marzof/fridge-staircase/railing_last_fixing_vsb.dxf

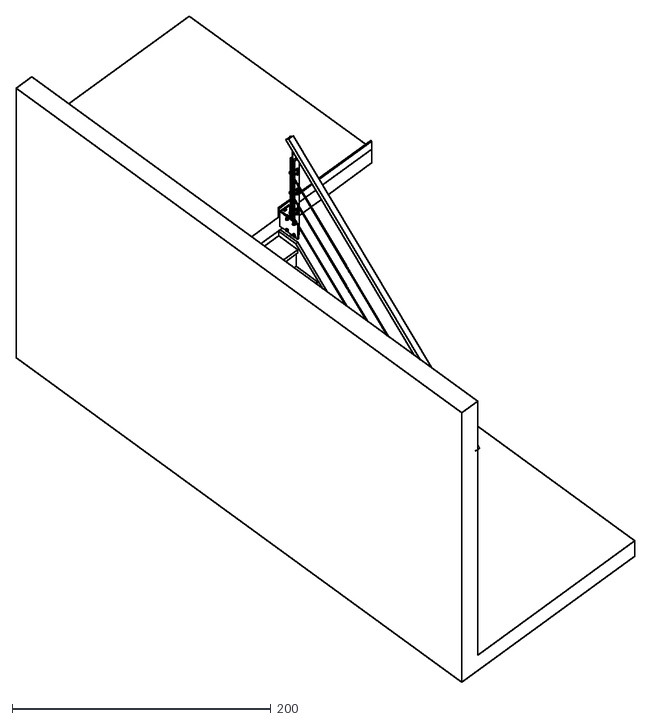
[picture p15: CAD file, 2017-08-27]
railing_last_fixing_vsb.dxf
478.4 x 514.9
