marzof/fridge-staircase/handrail_holder_vsb.dxf

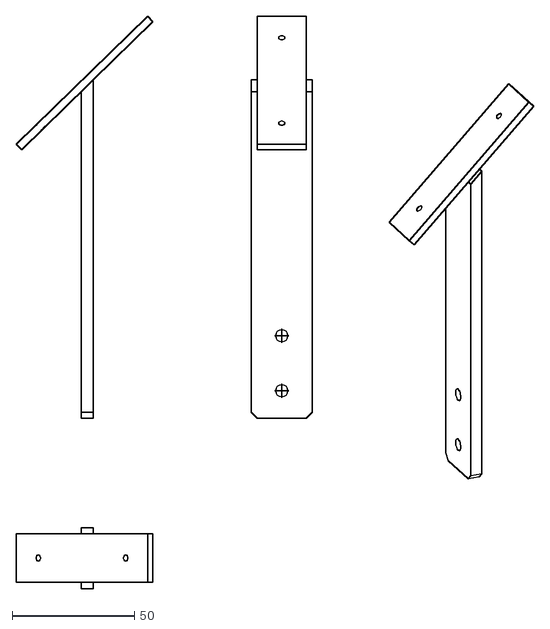
[picture p16: CAD file, 2017-08-27]
handrail_holder_vsb.dxf
211.8 x 234.3
