marzof/fridge-staircase/fasteners.fcstd

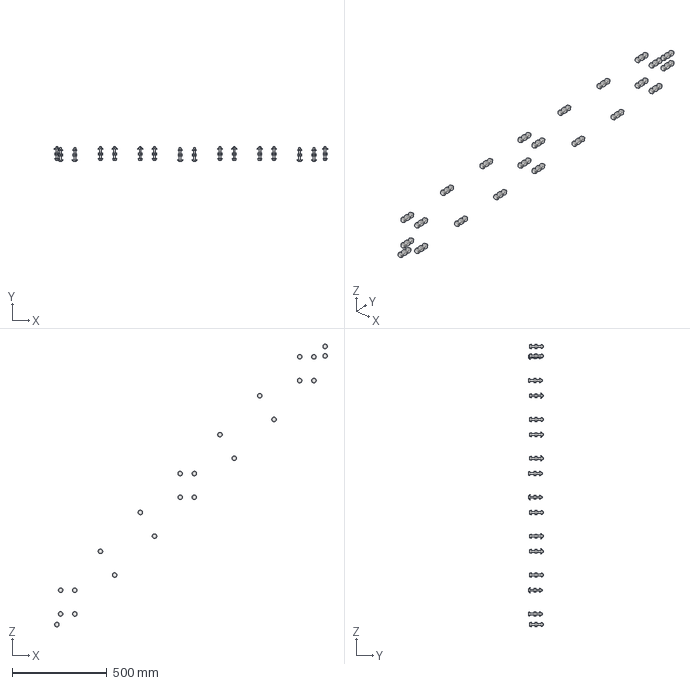
[picture p17: CAD file, 2017-08-27]
fasteners.fcstd
1438.8 x 78.4 x 1491.0 mm
