marzof/fridge-staircase/railing_wood_vsb.dxf

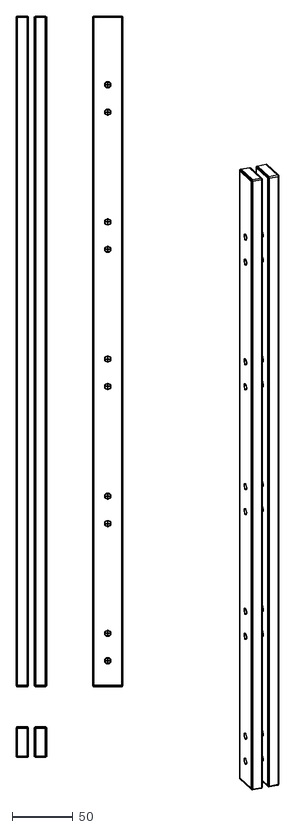
[picture p18: CAD file, 2017-08-27]
railing_wood_vsb.dxf
215.5 x 634.6
