marzof/fridge-staircase/railing_last.fcstd

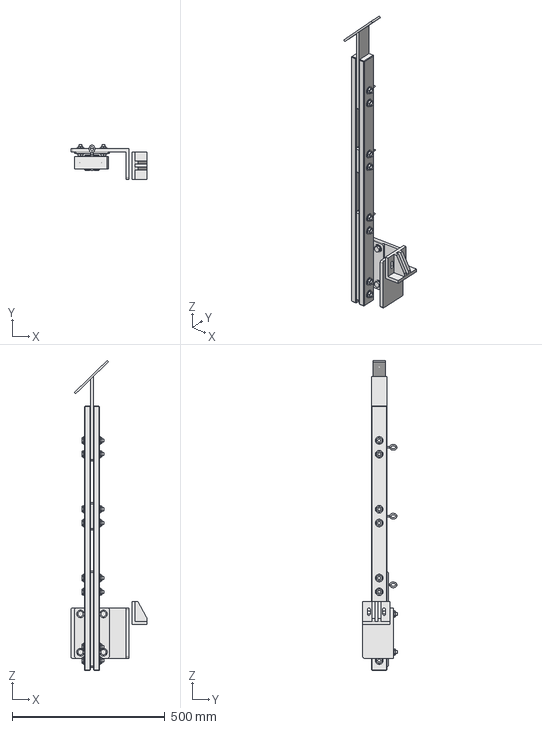
[picture p19: CAD file, 2017-08-27]
railing_last.fcstd
250.0 x 113.0 x 1014.1 mm
