marzof/fridge-staircase/fridge_box_door.fcstd

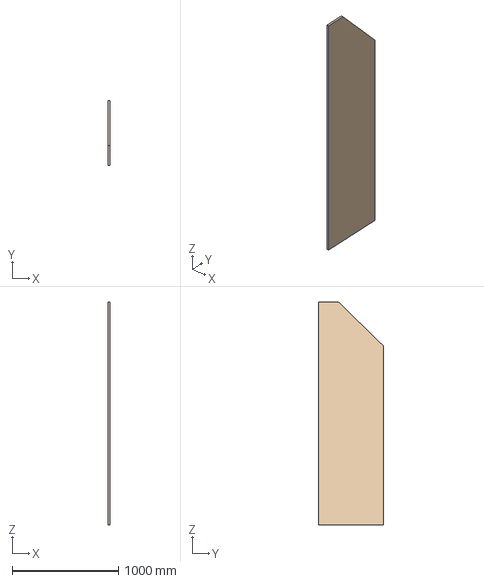
[picture p20: CAD file, 2017-08-27]
fridge_box_door.fcstd
18.0 x 610.0 x 2095.0 mm
