marzof/fridge-staircase/ropes.fcstd

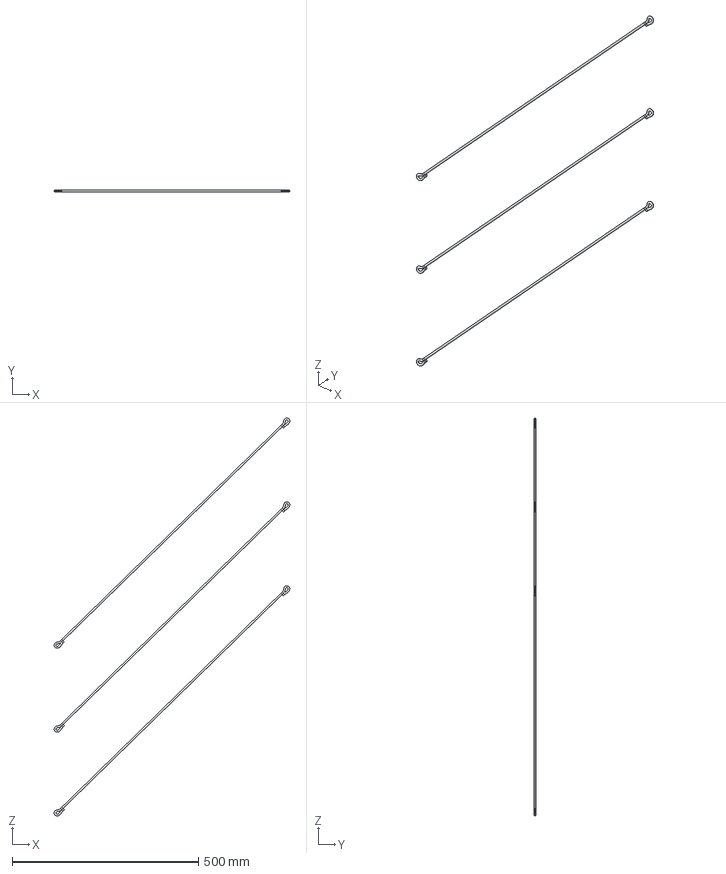
[picture p21: CAD file, 2017-08-27]
ropes.fcstd
632.3 x 5.00 x 1067.7 mm
