marzof/fridge-staircase/stair_profile.fcstd

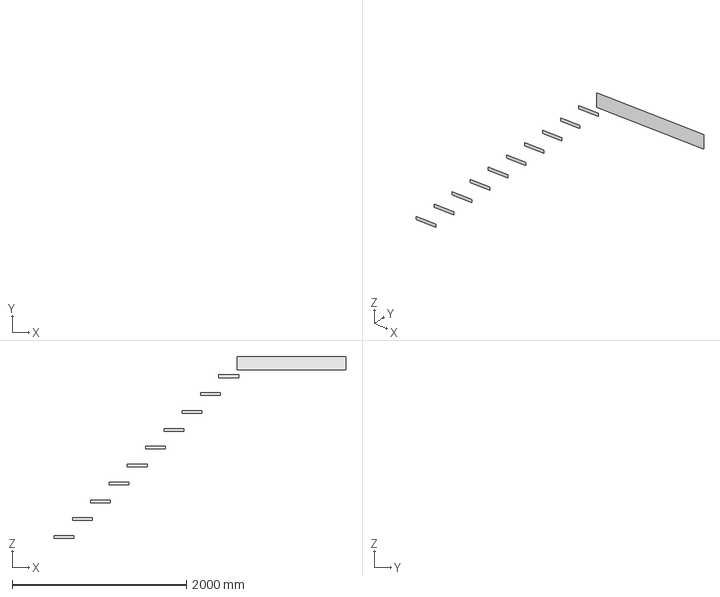
[picture p22: CAD file, 2017-08-27]
stair_profile.fcstd
3350.0 x 6.5e-14 x 2090.0 mm
