marzof/fridge-staircase/railing_front_hdn.dxf

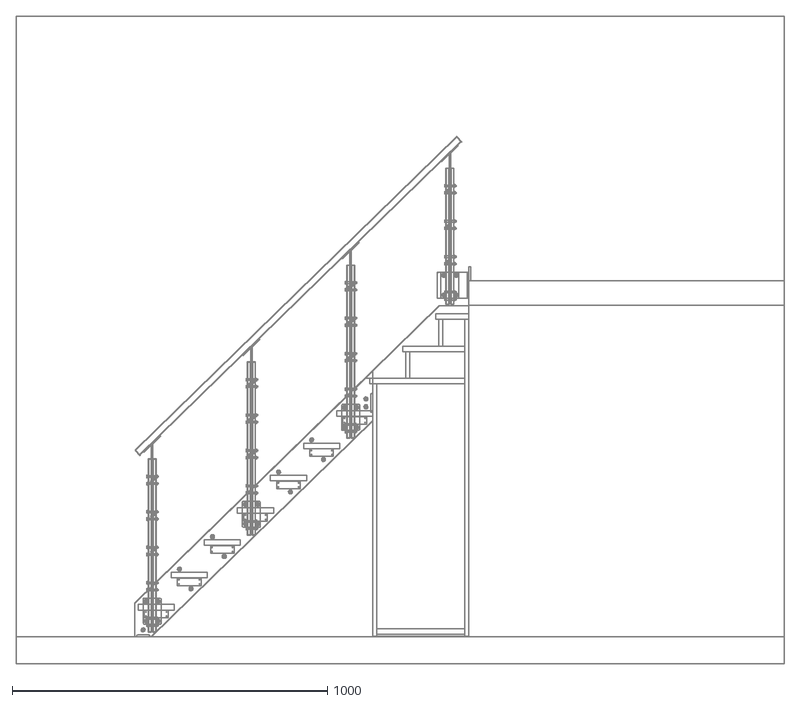
[picture p23: CAD file, 2017-08-27]
railing_front_hdn.dxf
2437.5 x 2056.1
