marzof/fridge-staircase/railing_rear_vsb.dxf

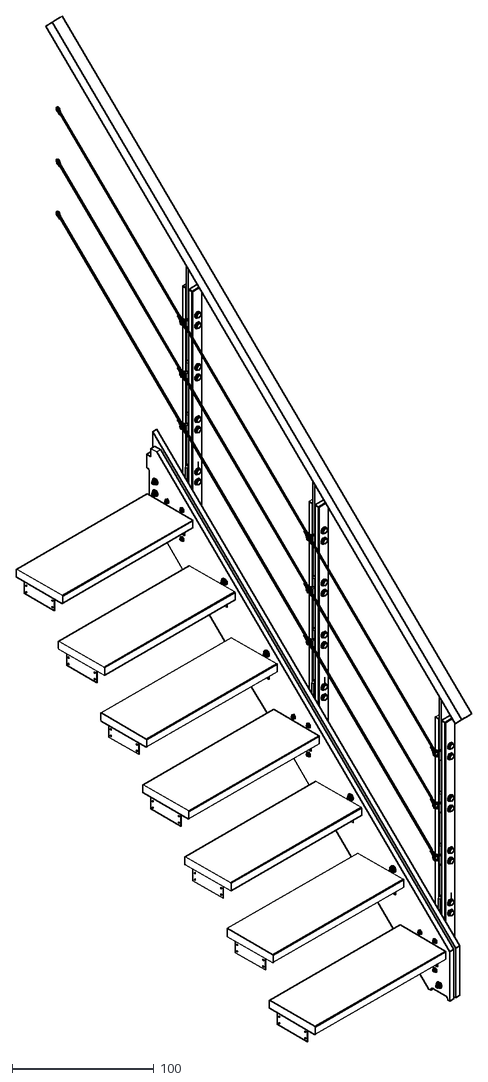
[picture p24: CAD file, 2017-08-27]
railing_rear_vsb.dxf
320.9 x 722.7
