marzof/fridge-staircase/plate.fcstd

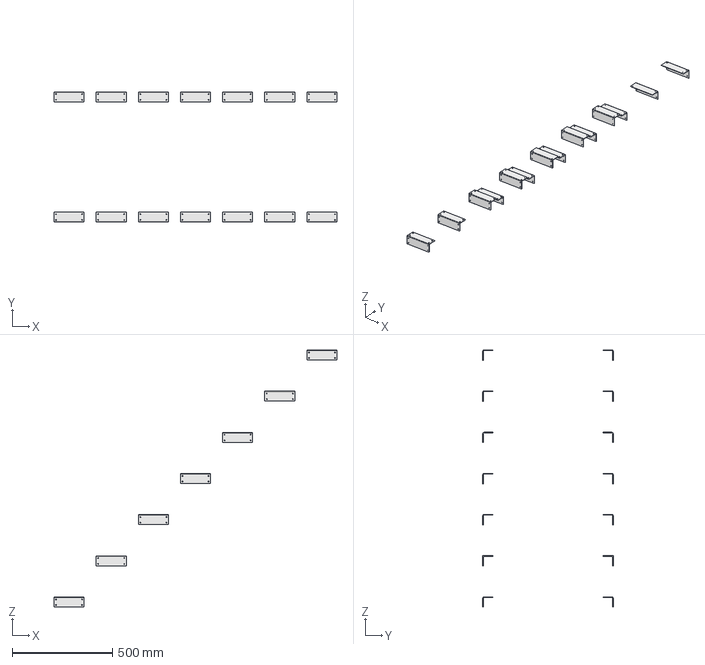
[picture p25: CAD file, 2017-08-27]
plate.fcstd
1410.0 x 650.0 x 1280.0 mm
