marzof/fridge-staircase/railing_wood_hdn.dxf

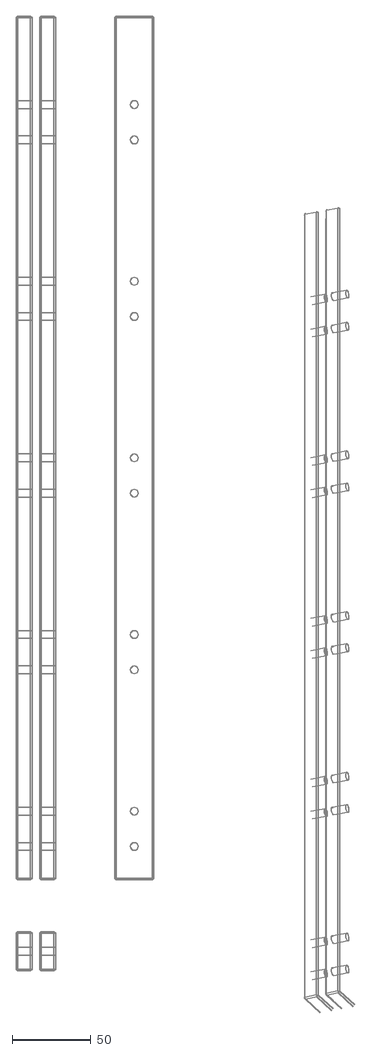
[picture p26: CAD file, 2017-08-27]
railing_wood_hdn.dxf
215.5 x 634.6
