marzof/fridge-staircase/railing_last_elements_hdn.dxf

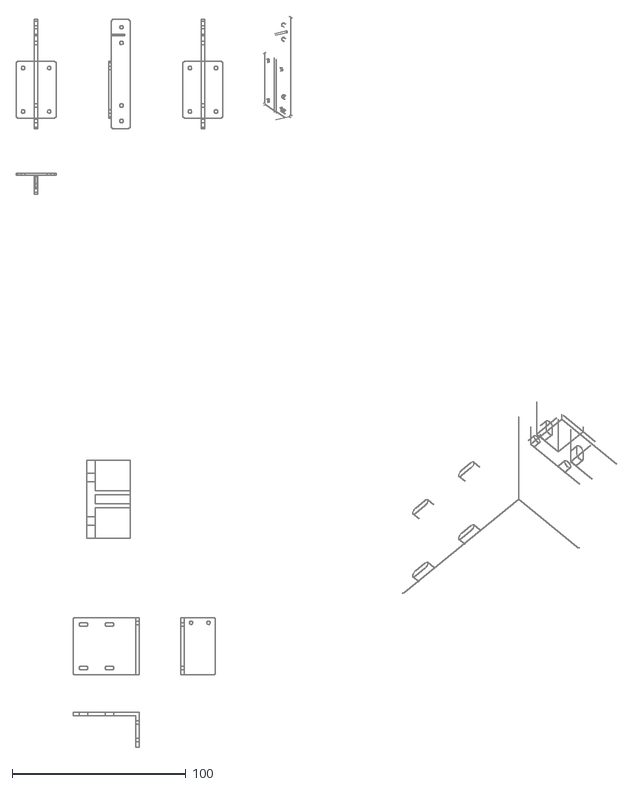
[picture p27: CAD file, 2017-08-27]
railing_last_elements_hdn.dxf
345.8 x 420.8
