marzof/fridge-staircase/railing_last_elements_vsb.dxf

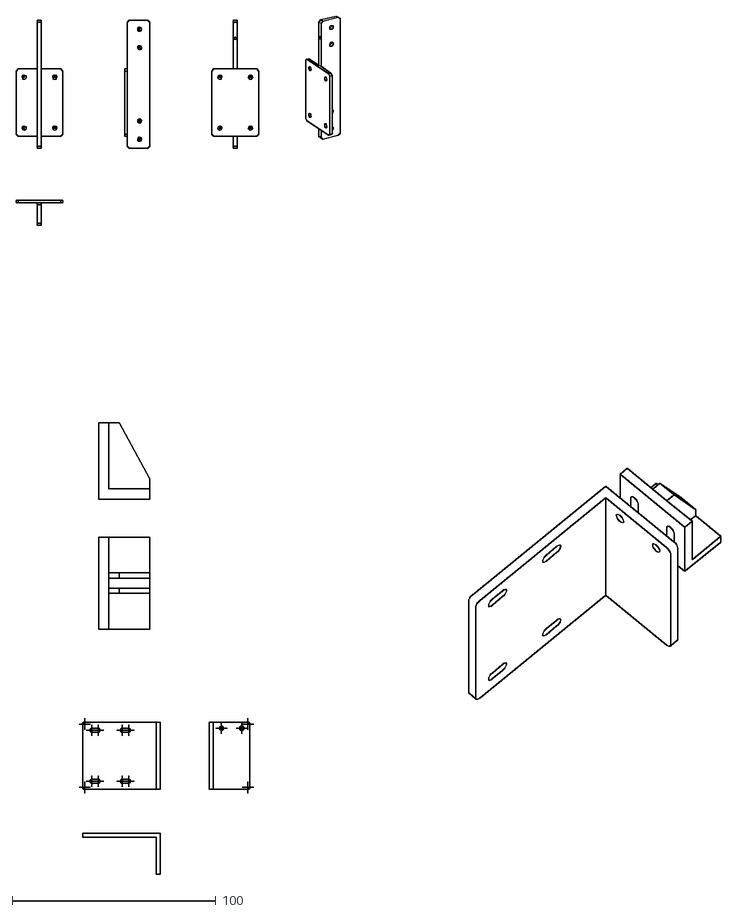
[picture p28: CAD file, 2017-08-27]
railing_last_elements_vsb.dxf
345.8 x 420.8
