marzof/fridge-staircase/railing_plate_hdn.dxf

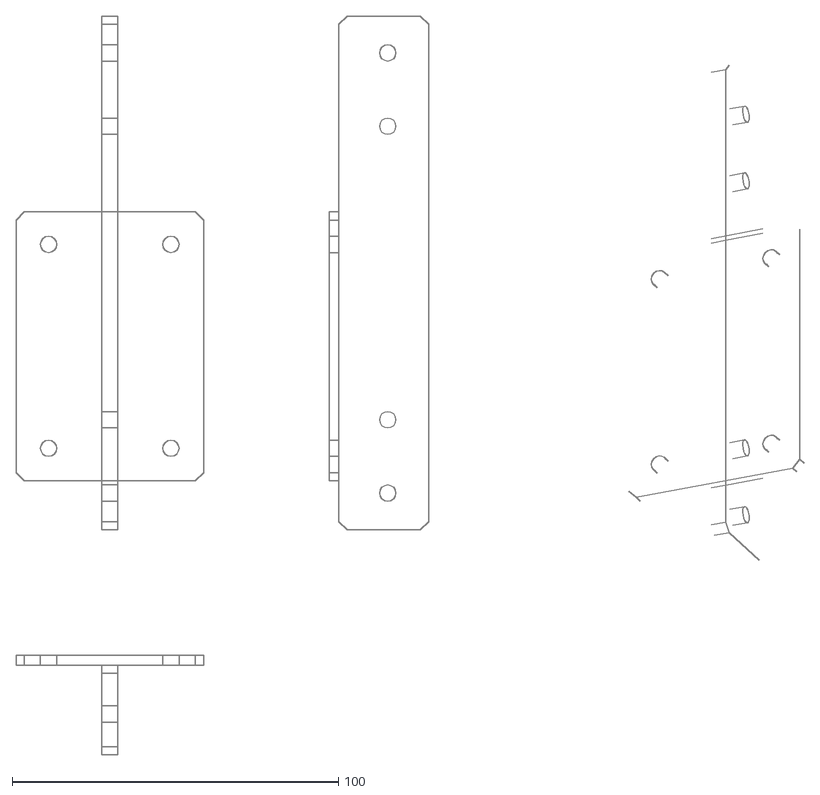
[picture p29: CAD file, 2017-08-27]
railing_plate_hdn.dxf
241.6 x 226.5
