marzof/fridge-staircase/railing_last_fixing_hdn.dxf

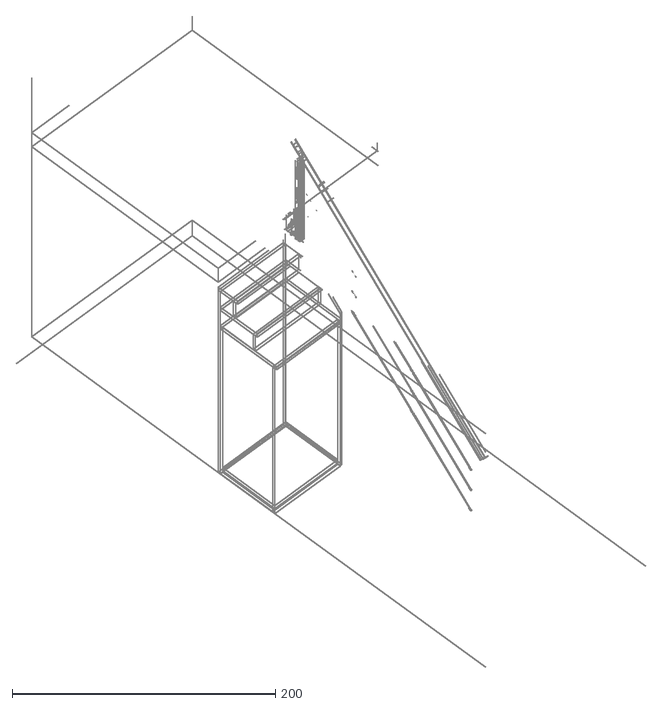
[picture p30: CAD file, 2017-08-27]
railing_last_fixing_hdn.dxf
478.4 x 494.3
