marzof/fridge-staircase/railing_last_wood_hdn.dxf

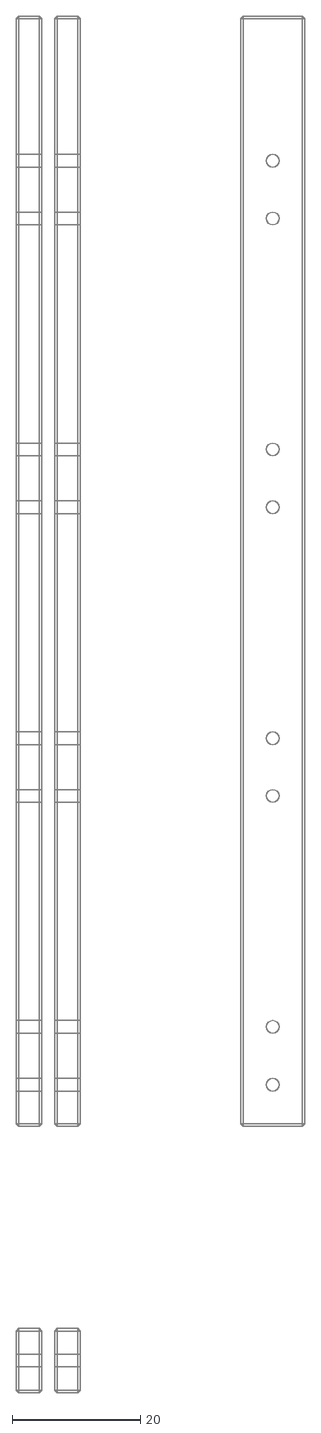
[picture p31: CAD file, 2017-08-27]
railing_last_wood_hdn.dxf
45.0 x 214.5
