marzof/fridge-staircase/loft_ropes.fcstd

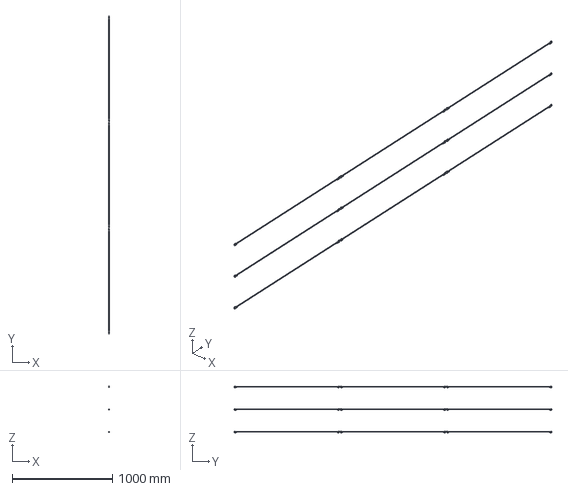
[picture p32: CAD file, 2017-08-27]
loft_ropes.fcstd
5.00 x 3176.2 x 467.0 mm
