marzof/fridge-staircase/railing_wood.fcstd

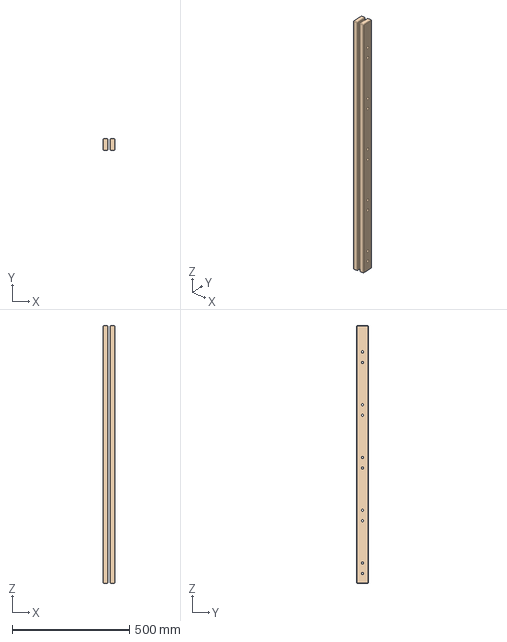
[picture p33: CAD file, 2017-08-27]
railing_wood.fcstd
50.0 x 50.0 x 1100.0 mm
