marzof/fridge-staircase/railing_last_wood.fcstd

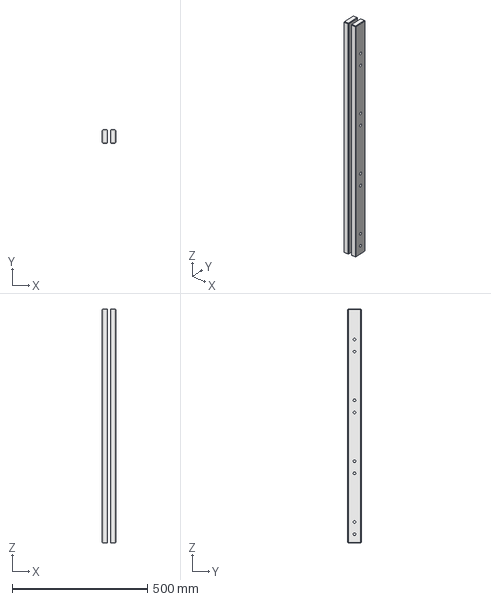
[picture p34: CAD file, 2017-08-27]
railing_last_wood.fcstd
50.0 x 50.0 x 865.0 mm
