marzof/fridge-staircase/railing_last_plate_hdn.dxf

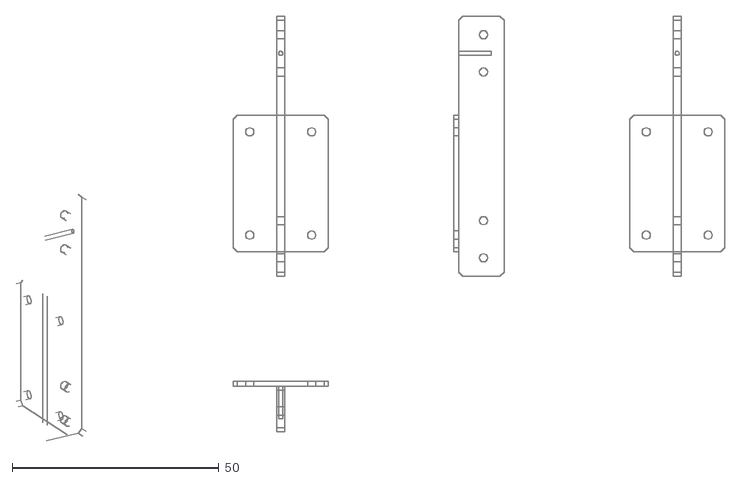
[picture p35: CAD file, 2017-08-27]
railing_last_plate_hdn.dxf
171.5 x 102.8
