marzof/fridge-staircase/railing_dist_hdn.dxf

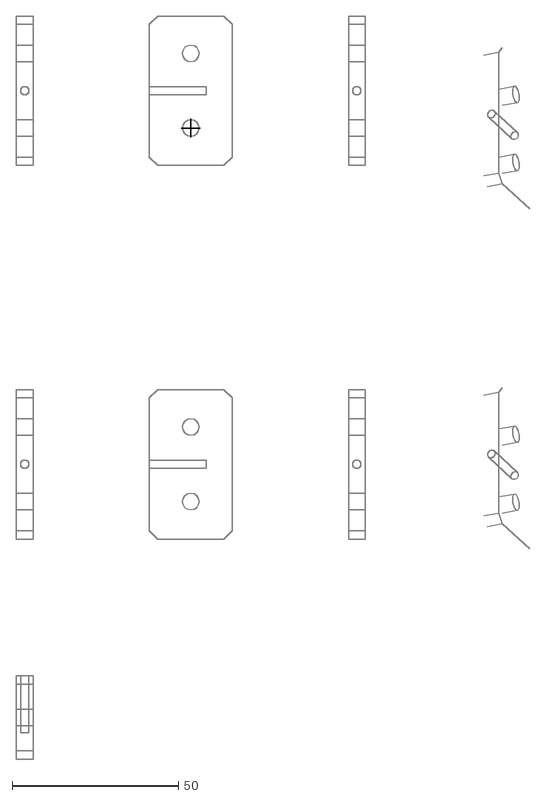
[picture p36: CAD file, 2017-08-27]
railing_dist_hdn.dxf
154.5 x 223.8
