marzof/fridge-staircase/handrail.fcstd

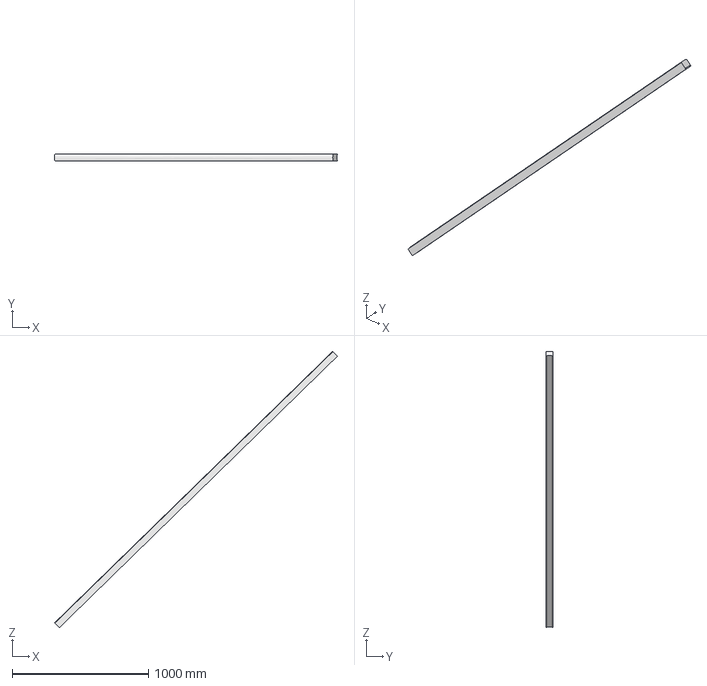
[picture p37: CAD file, 2017-08-27]
handrail.fcstd
2074.3 x 50.0 x 2026.6 mm
