marzof/fridge-staircase/railing_plate.fcstd

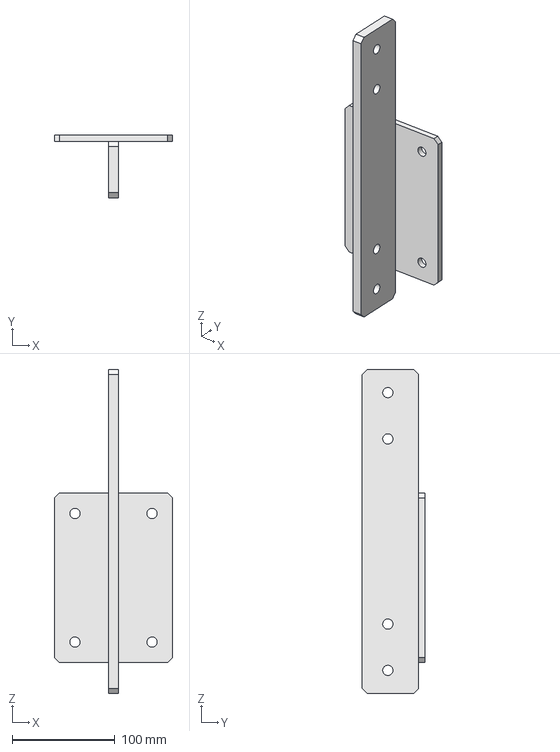
[picture p38: CAD file, 2017-08-27]
railing_plate.fcstd
115.0 x 61.0 x 315.0 mm
