marzof/fridge-staircase/step.fcstd

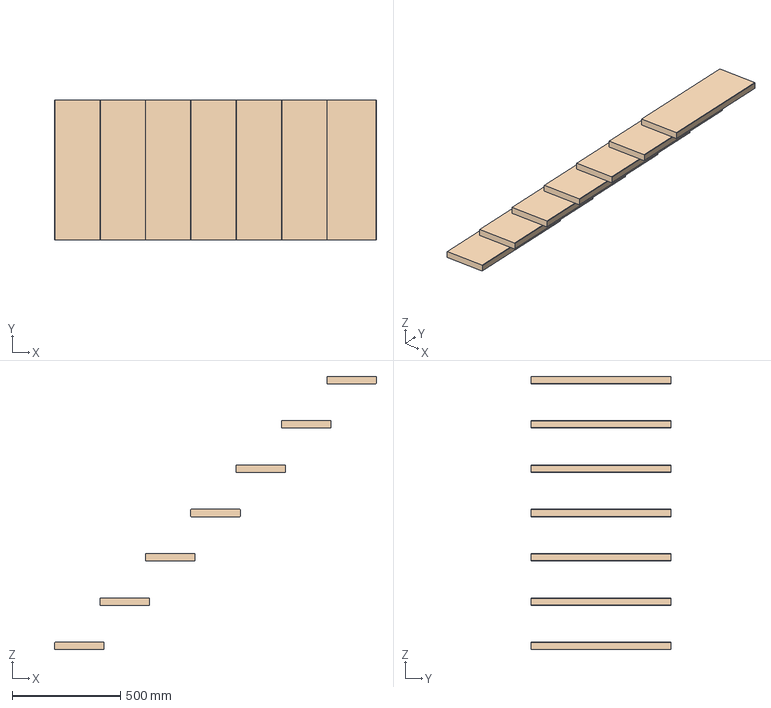
[picture p39: CAD file, 2017-08-27]
step.fcstd
1490.0 x 650.0 x 1265.0 mm
