marzof/fridge-staircase/railing_eyelet.fcstd

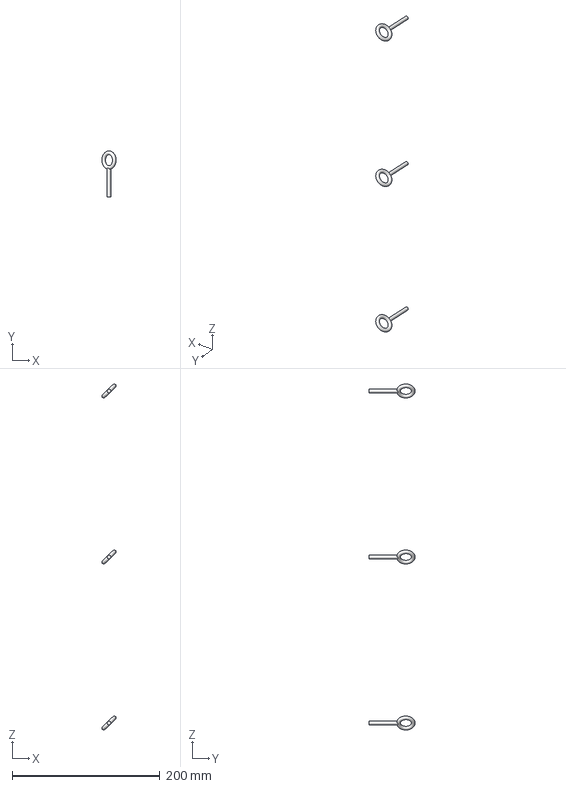
[picture p40: CAD file, 2017-08-27]
railing_eyelet.fcstd
19.3 x 62.5 x 469.0 mm
