marzof/fridge-staircase/loft_railing_element.fcstd

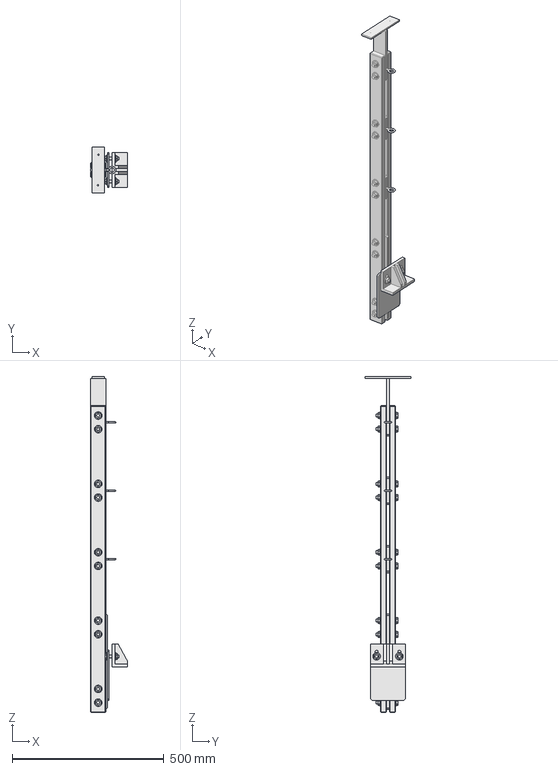
[picture p41: CAD file, 2017-08-27]
loft_railing_element.fcstd
121.0 x 150.0 x 1106.0 mm
