marzof/fridge-staircase/beam.fcstd

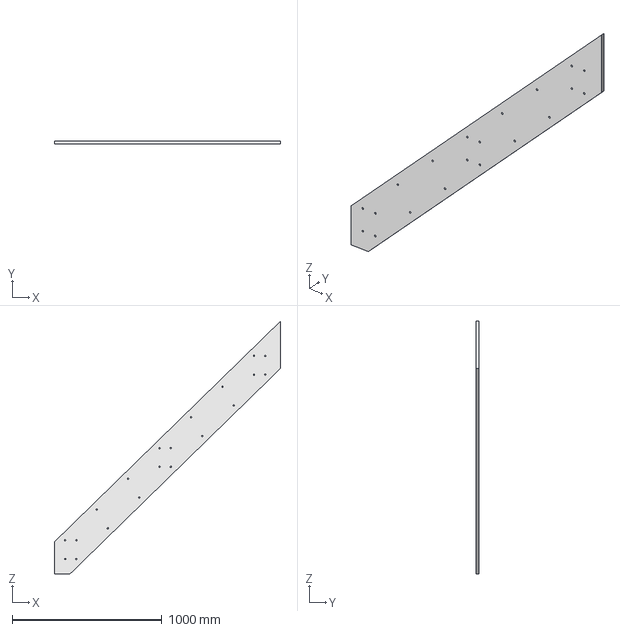
[picture p42: CAD file, 2017-08-27]
beam.fcstd
1510.0 x 20.0 x 1687.5 mm
