marzof/fridge-staircase/railing_front_vsb.dxf

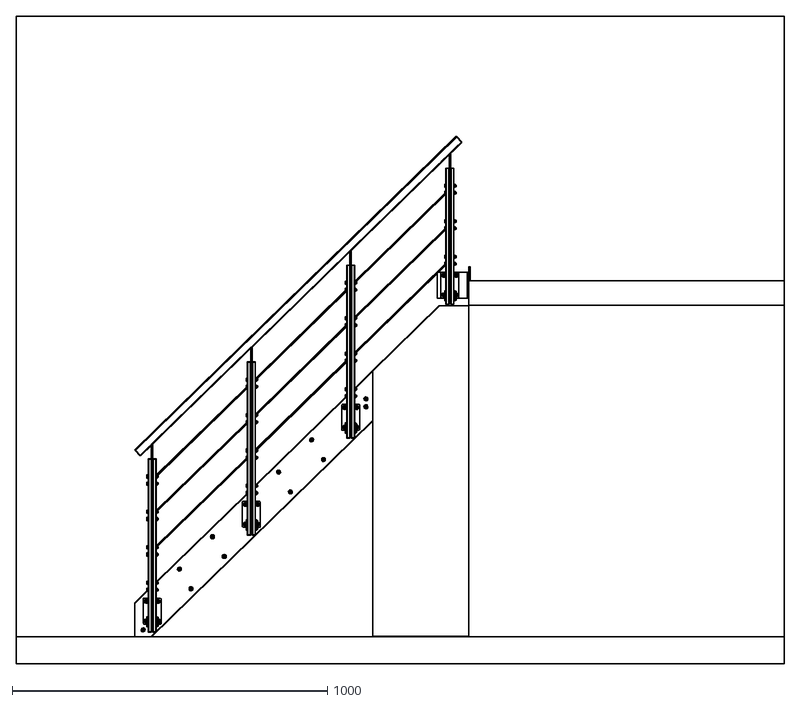
[picture p43: CAD file, 2017-08-27]
railing_front_vsb.dxf
2437.5 x 2056.1
