marzof/fridge-staircase/railing_dist_vsb.dxf

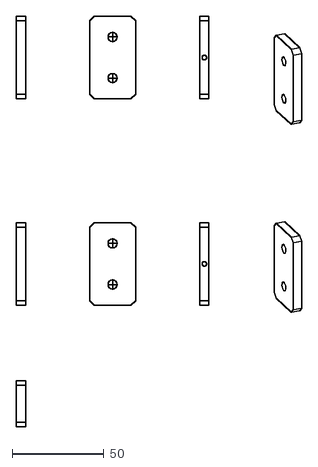
[picture p44: CAD file, 2017-08-27]
railing_dist_vsb.dxf
155.5 x 223.7
