marzof/fridge-staircase/railing_last_steel.fcstd

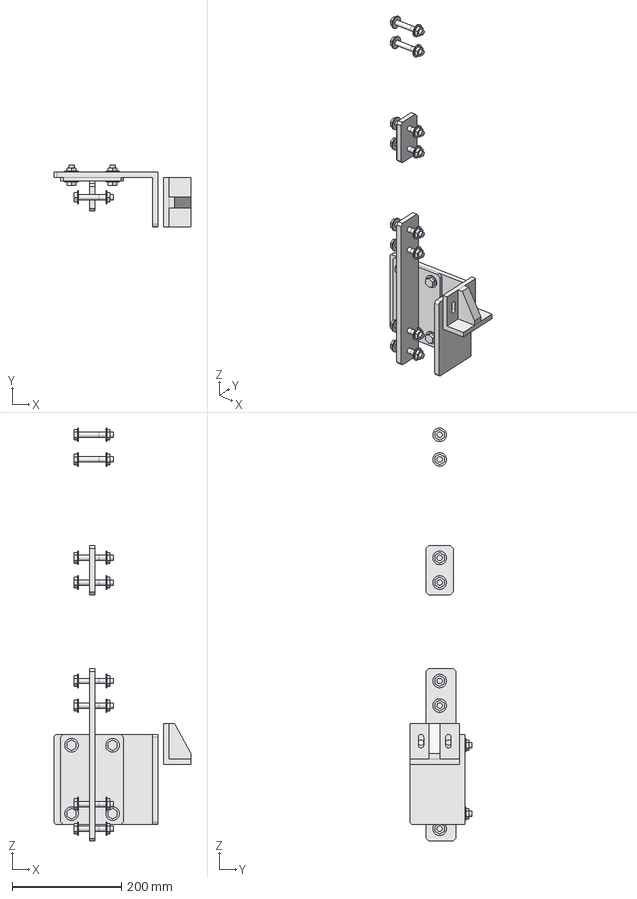
[picture p45: CAD file, 2017-08-27]
railing_last_steel.fcstd
250.0 x 113.0 x 755.0 mm
