marzof/fridge-staircase/railing_dist.fcstd

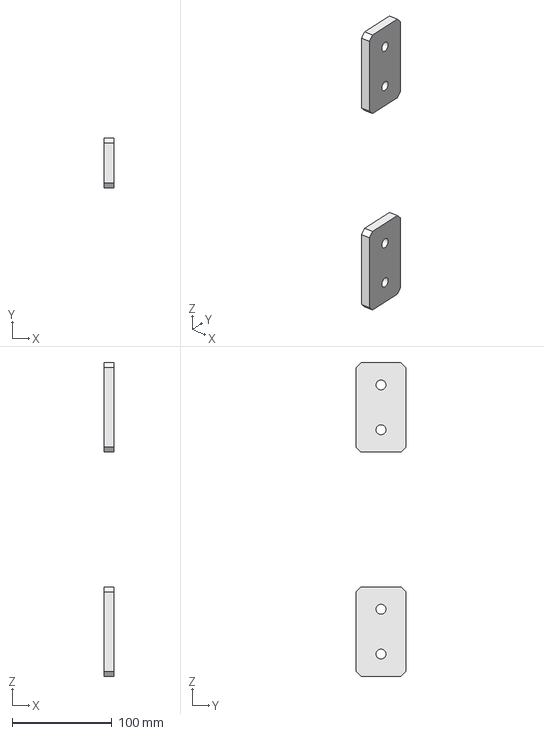
[picture p46: CAD file, 2017-08-27]
railing_dist.fcstd
10.0 x 50.0 x 315.0 mm
