marzof/fridge-staircase/room.fcstd

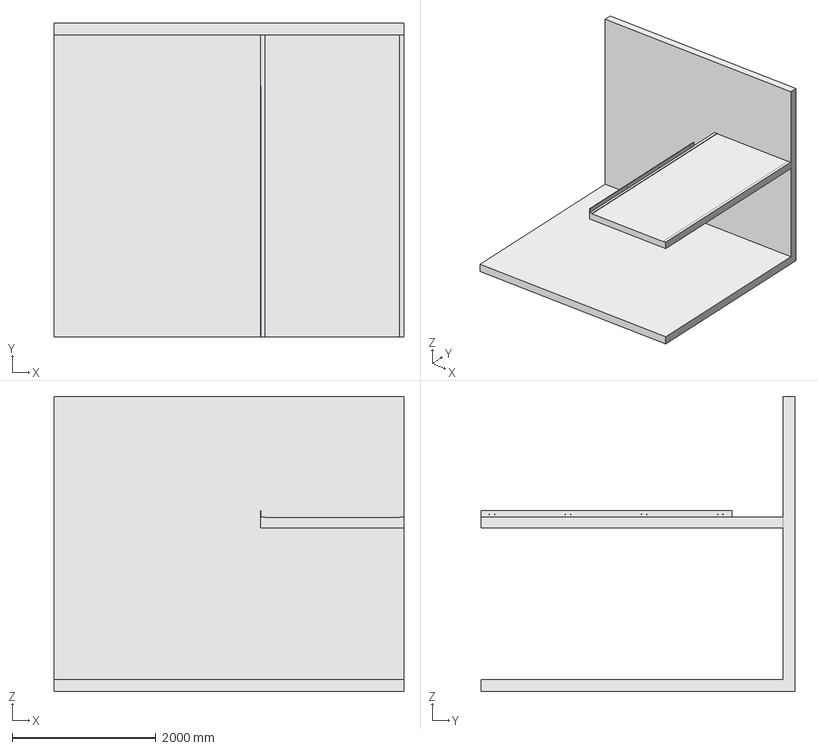
[picture p47: CAD file, 2017-08-27]
room.fcstd
4875.0 x 4375.4 x 4112.1 mm
