marzof/fridge-staircase/railing_rear_hdn.dxf

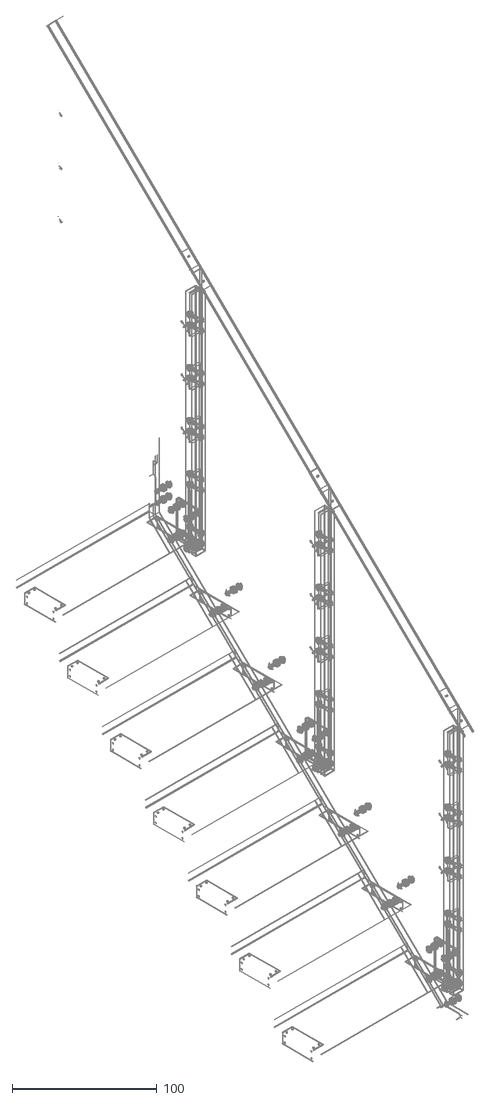
[picture p48: CAD file, 2017-08-27]
railing_rear_hdn.dxf
316.2 x 722.5
