marzof/fridge-staircase/railing_plate_vsb.dxf

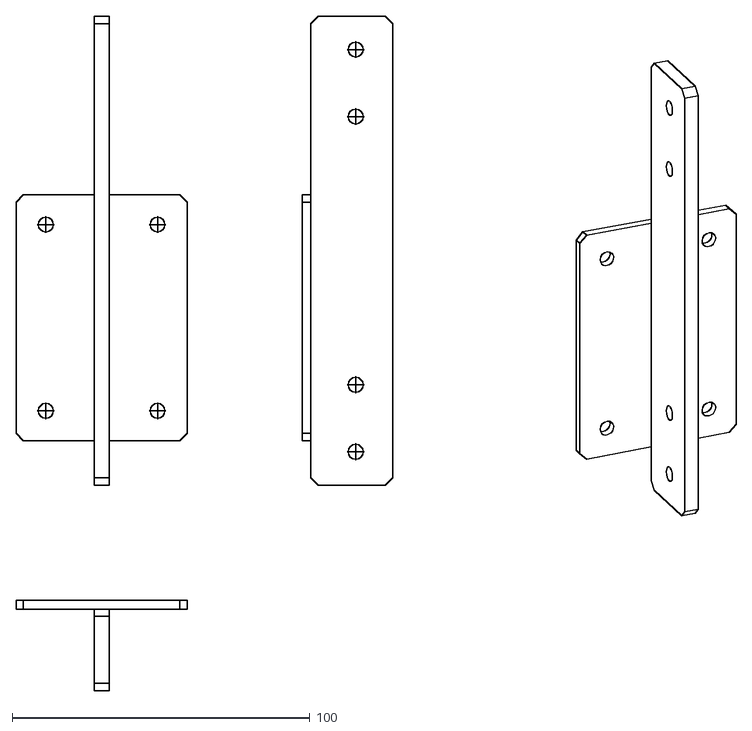
[picture p49: CAD file, 2017-08-27]
railing_plate_vsb.dxf
241.6 x 226.5
