marzof/fridge-staircase/railing_last_plate_vsb.dxf

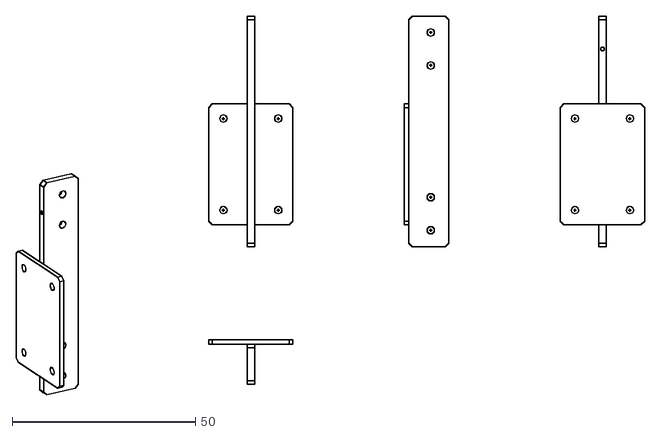
[picture p50: CAD file, 2017-08-27]
railing_last_plate_vsb.dxf
171.5 x 103.5
