marzof/fridge-staircase/handrail_holder.fcstd

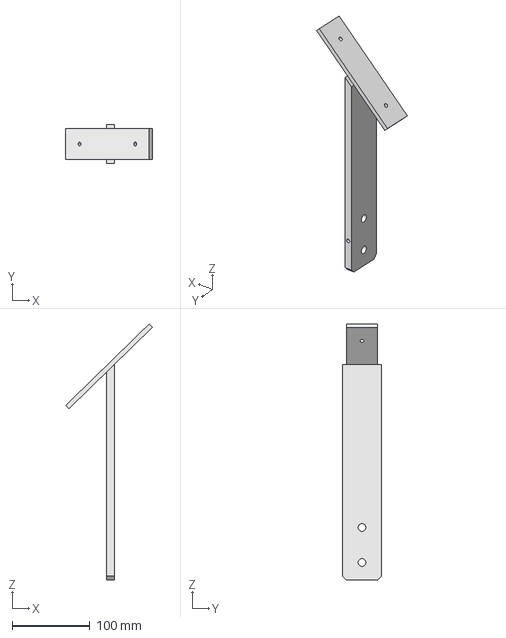
[picture p51: CAD file, 2017-08-27]
handrail_holder.fcstd
111.5 x 50.0 x 329.1 mm
