marzof/fridge-staircase/handrail_holder_hdn.dxf

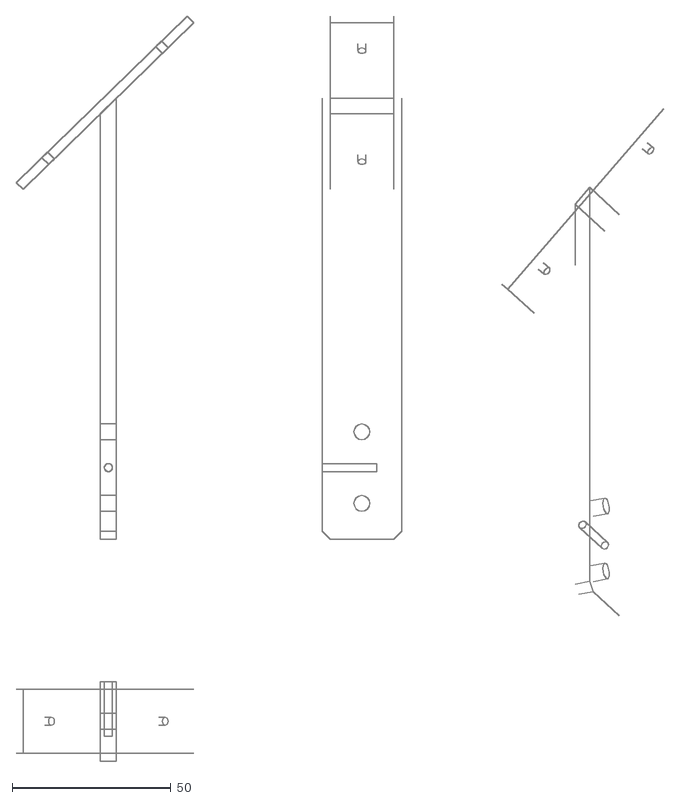
[picture p52: CAD file, 2017-08-27]
handrail_holder_hdn.dxf
203.6 x 234.3
